HarmonicAsh/Flinders_OpenCat/CAD components/Pi3B_spacer_R_switch.stl

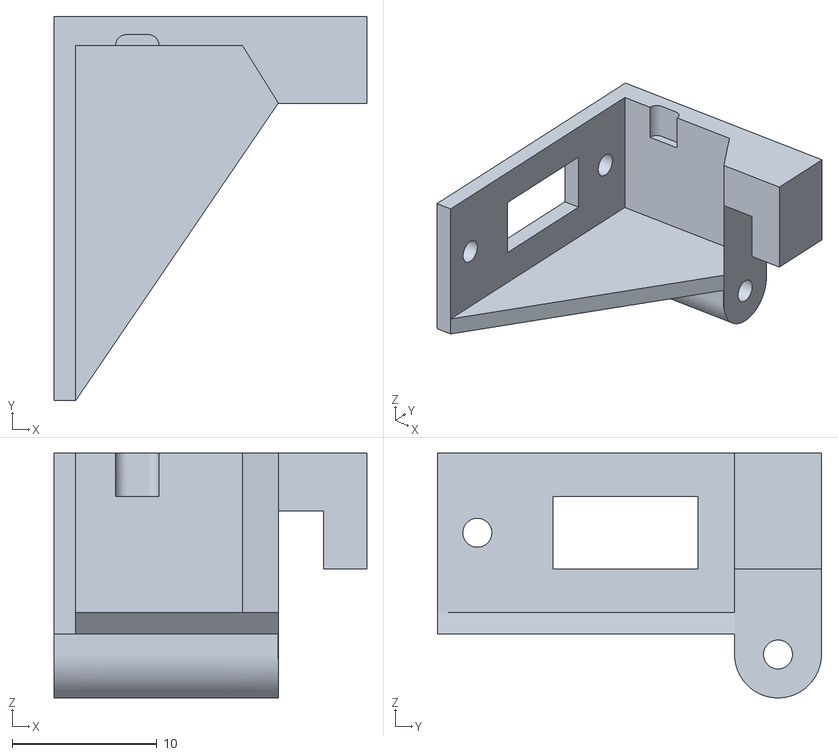
[picture p21: CAD file, 2023-02-03]
CAD components/Pi3B_spacer_R_switch.stl
21.6 x 26.5 x 16.9
