HarmonicAsh/Flinders_OpenCat/CAD components/battery mount rear.stl

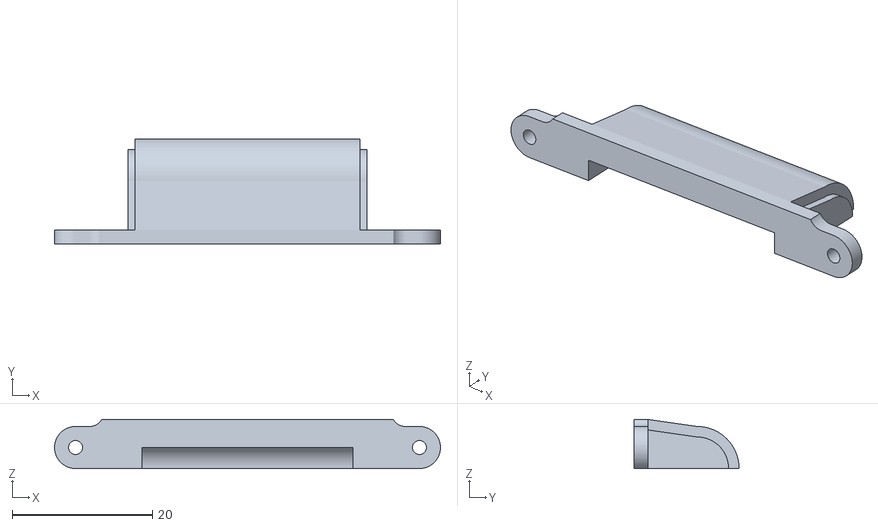
[picture p22: CAD file, 2023-01-31]
CAD components/battery mount rear.stl
55.0 x 15.0 x 7.00
