HarmonicAsh/Flinders_OpenCat/CAD components/NybbleDIY/Controller_Mount.stl

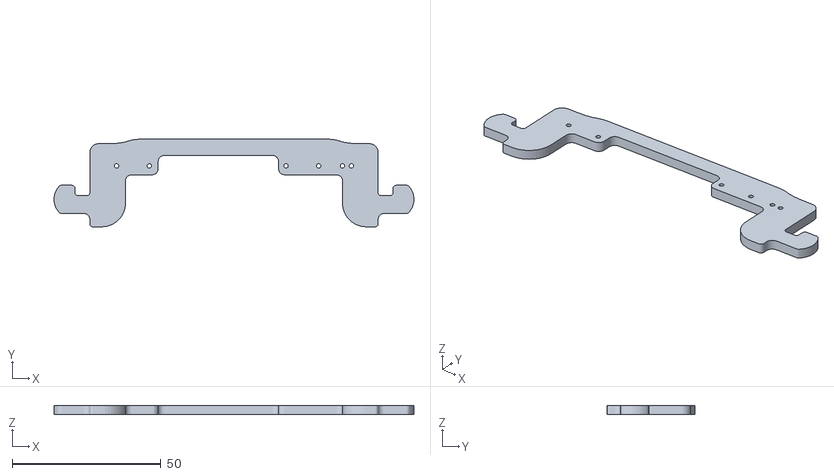
[picture p23: CAD file, 2023-01-29]
CAD components/NybbleDIY/Controller_Mount.stl
121.1 x 29.5 x 3.00
