HarmonicAsh/Flinders_OpenCat/CAD components/Battery mount front.stl

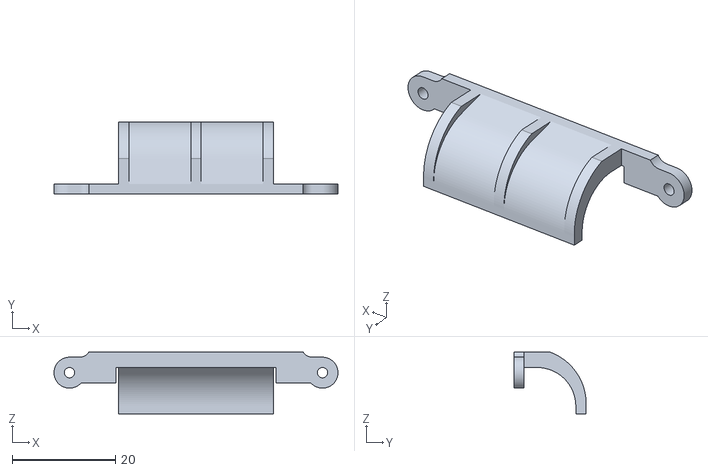
[picture p24: CAD file, 2023-01-31]
CAD components/Battery mount front.stl
55.0 x 14.0 x 12.0
