HarmonicAsh/Flinders_OpenCat/CAD components/NybbleDIY/Whiskers.stl

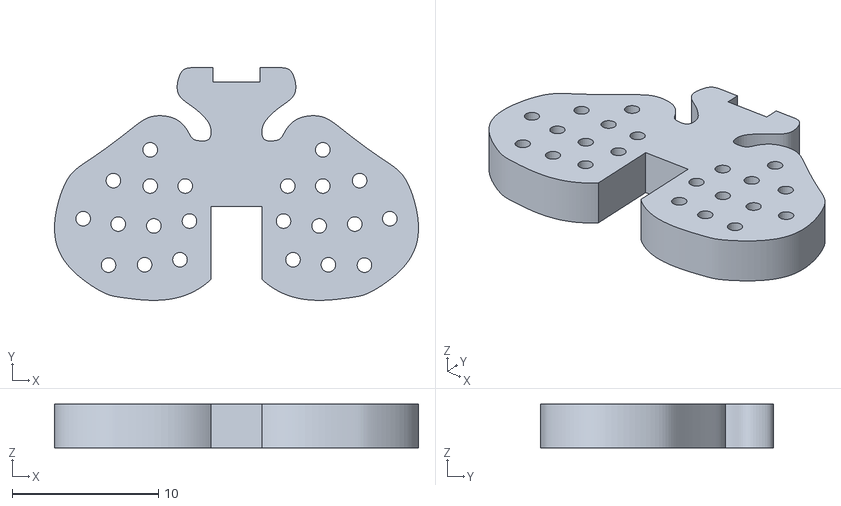
[picture p25: CAD file, 2023-01-29]
CAD components/NybbleDIY/Whiskers.stl
24.9 x 15.9 x 3.00
