HarmonicAsh/Flinders_OpenCat/CAD components/Base_modded.stl

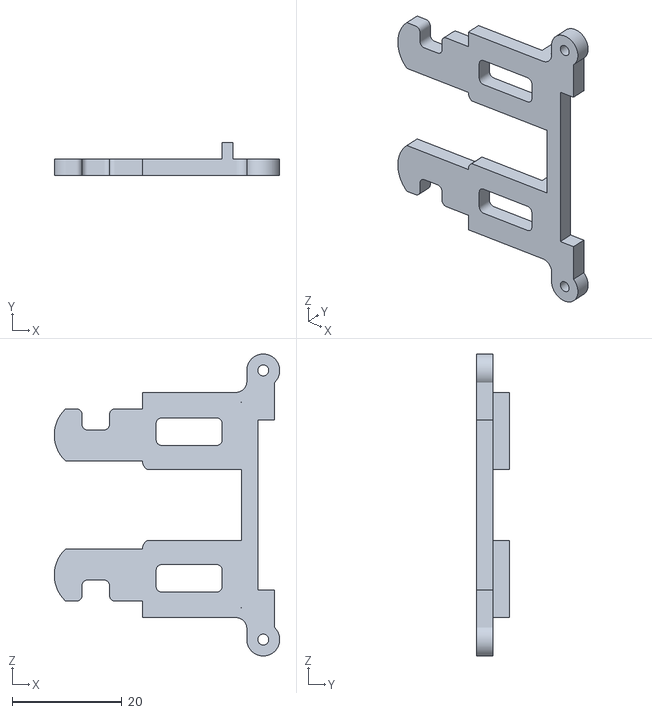
[picture p26: CAD file, 2023-01-31]
CAD components/Base_modded.stl
41.1 x 6.00 x 55.0
