HarmonicAsh/Flinders_OpenCat/CAD components/NybbleDIY/Thigh_Test_4.9mm.stl

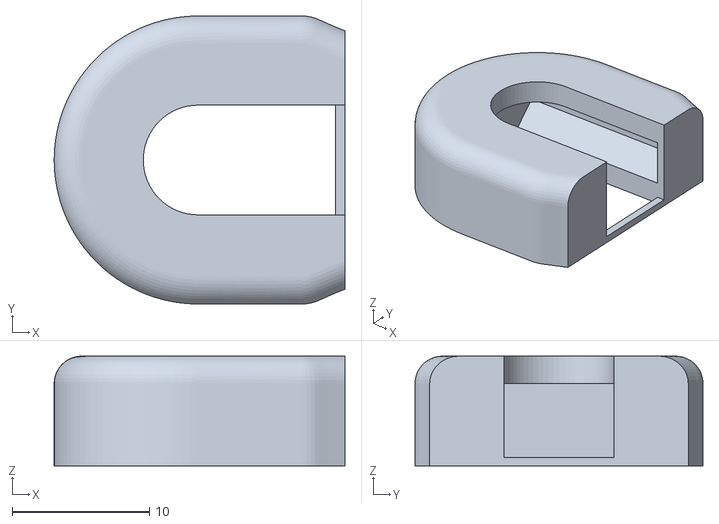
[picture p27: CAD file, 2023-01-29]
CAD components/NybbleDIY/Thigh_Test_4.9mm.stl
21.2 x 21.0 x 8.00
