HarmonicAsh/Flinders_OpenCat/CAD components/Pi3B_spacer_R.stl

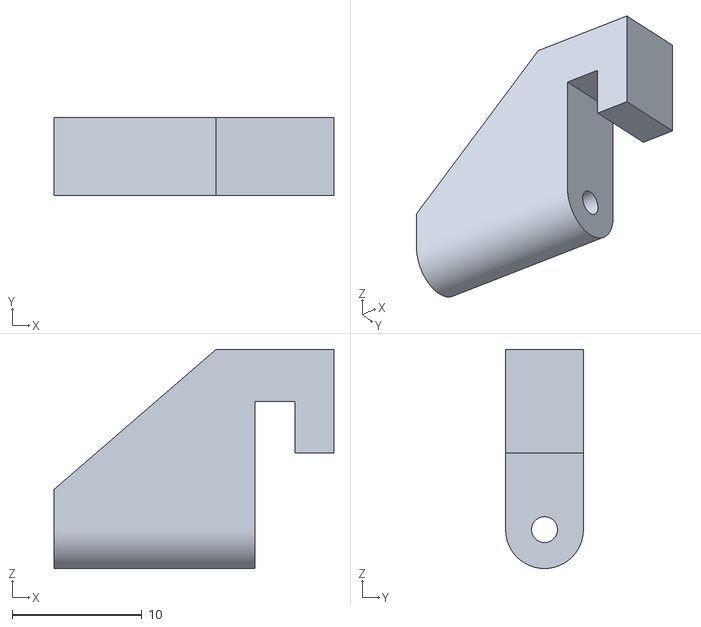
[picture p28: CAD file, 2023-01-30]
CAD components/Pi3B_spacer_R.stl
21.6 x 6.00 x 16.9
