HarmonicAsh/Flinders_OpenCat/CAD components/Battery_holder_upper.stl

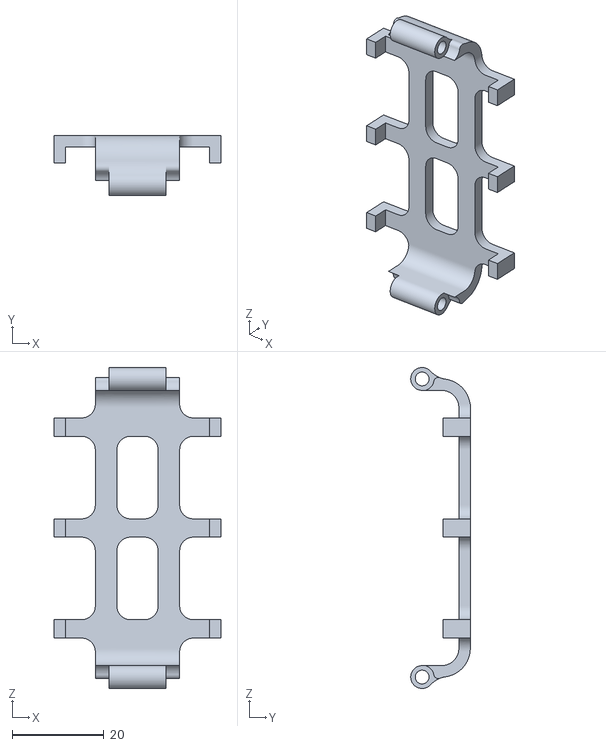
[picture p29: CAD file, 2023-01-30]
CAD components/Battery_holder_upper.stl
36.4 x 13.0 x 70.0
