HarmonicAsh/Flinders_OpenCat/CAD components/NybbleDIY/Neck_Side_Plate.stl

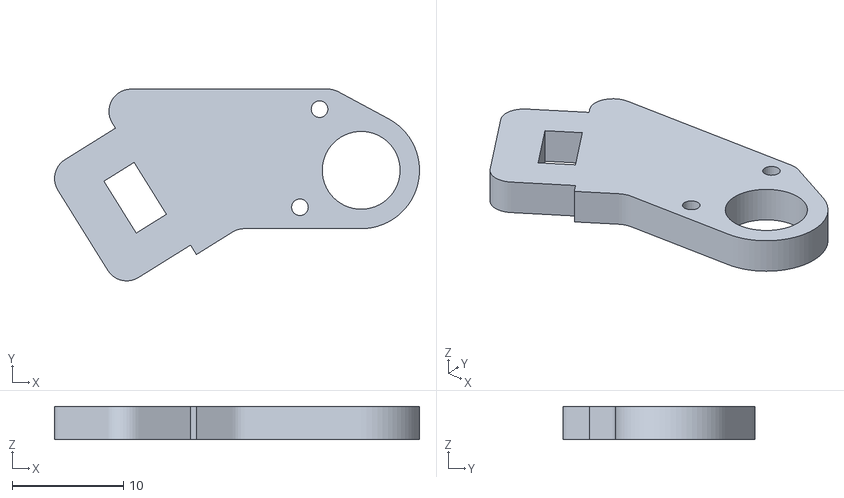
[picture p30: CAD file, 2023-01-29]
CAD components/NybbleDIY/Neck_Side_Plate.stl
32.8 x 17.3 x 3.00
