HarmonicAsh/Flinders_OpenCat/CAD components/Battery_holer_lower.stl

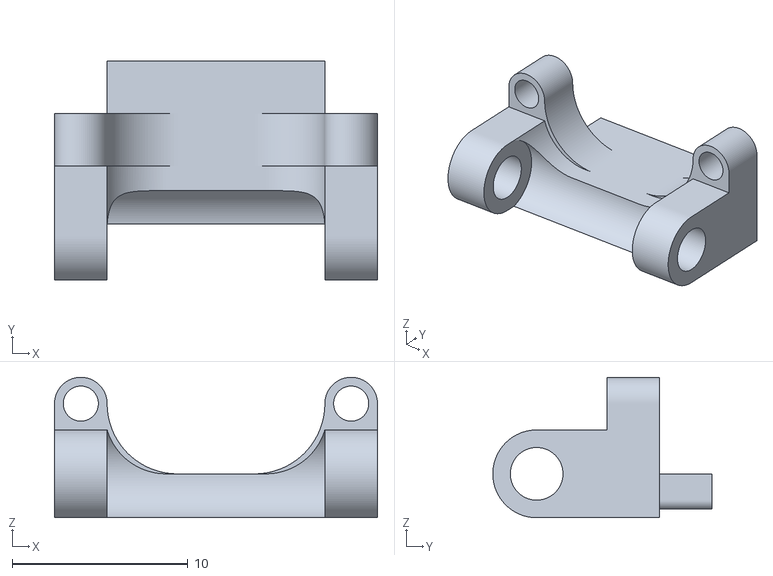
[picture p31: CAD file, 2023-01-30]
CAD components/Battery_holer_lower.stl
18.4 x 12.5 x 8.00
