HarmonicAsh/Flinders_OpenCat/CAD components/NybbleDIY/Tail.stl

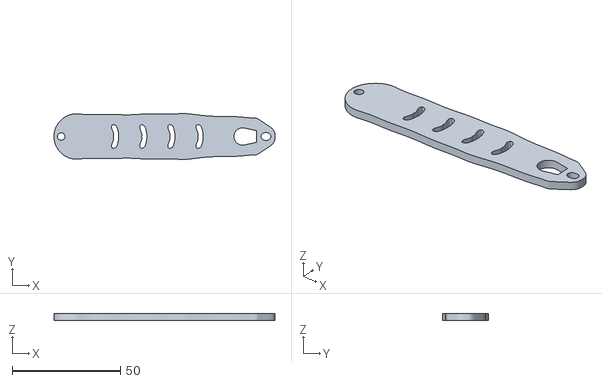
[picture p32: CAD file, 2023-01-29]
CAD components/NybbleDIY/Tail.stl
102.0 x 21.2 x 3.00
