HarmonicAsh/Flinders_OpenCat/CAD components/NybbleDIY/Chest_Hips.stl

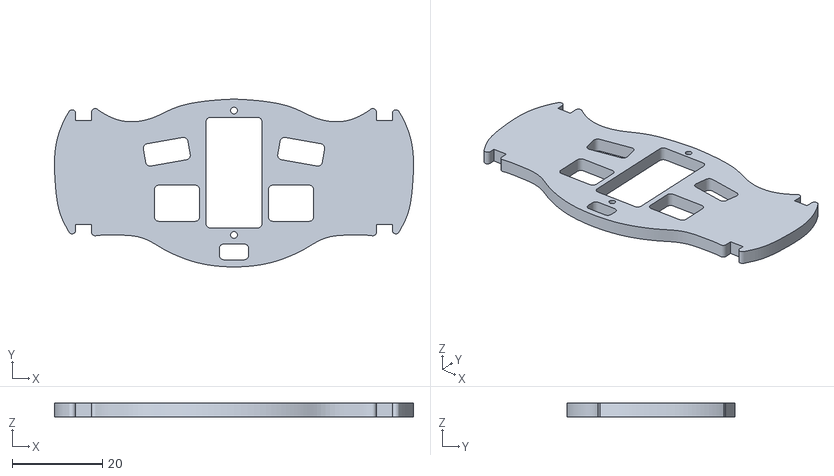
[picture p33: CAD file, 2023-01-29]
CAD components/NybbleDIY/Chest_Hips.stl
79.4 x 37.1 x 3.00
