HarmonicAsh/Flinders_OpenCat/CAD components/Pi_mount.stl

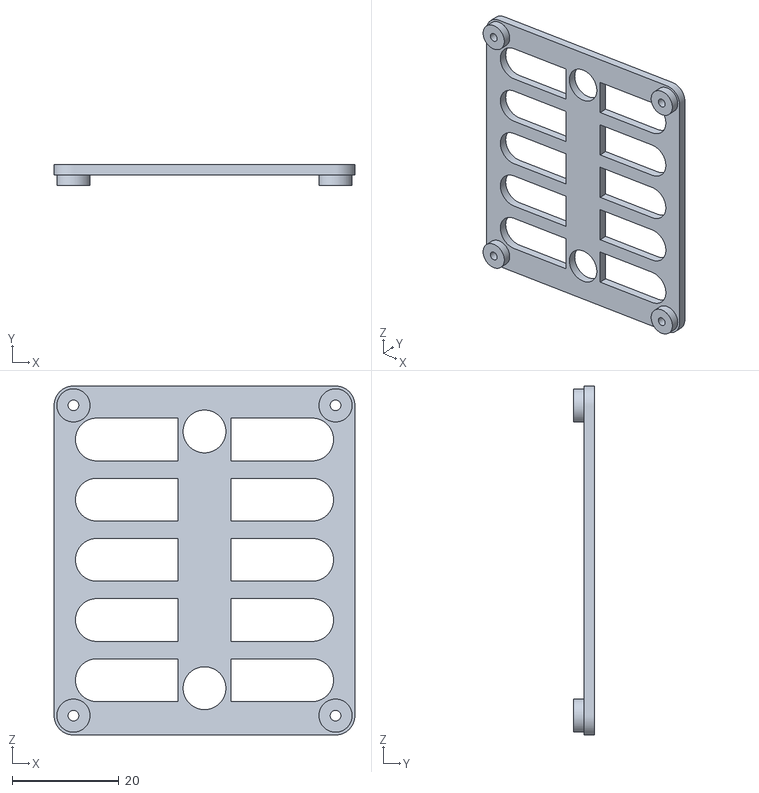
[picture p34: CAD file, 2023-01-29]
CAD components/Pi_mount.stl
56.2 x 4.00 x 65.2
