HarmonicAsh/Flinders_OpenCat/CAD components/NybbleDIY/BellyPlate.stl

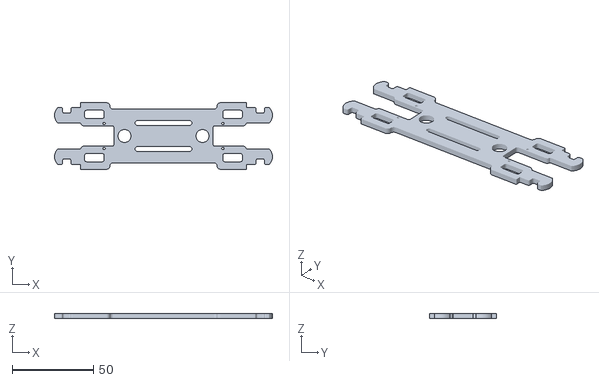
[picture p35: CAD file, 2023-01-29]
CAD components/NybbleDIY/BellyPlate.stl
134.1 x 41.0 x 3.00
