HarmonicAsh/Flinders_OpenCat/CAD components/Pi_lid.stl

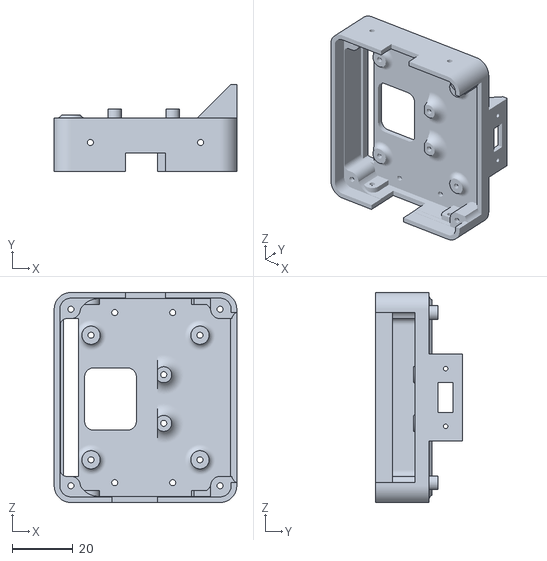
[picture p36: CAD file, 2023-01-29]
CAD components/Pi_lid.stl
60.0 x 28.5 x 69.0
