HarmonicAsh/Flinders_OpenCat/CAD components/NybbleDIY/Eyes.stl

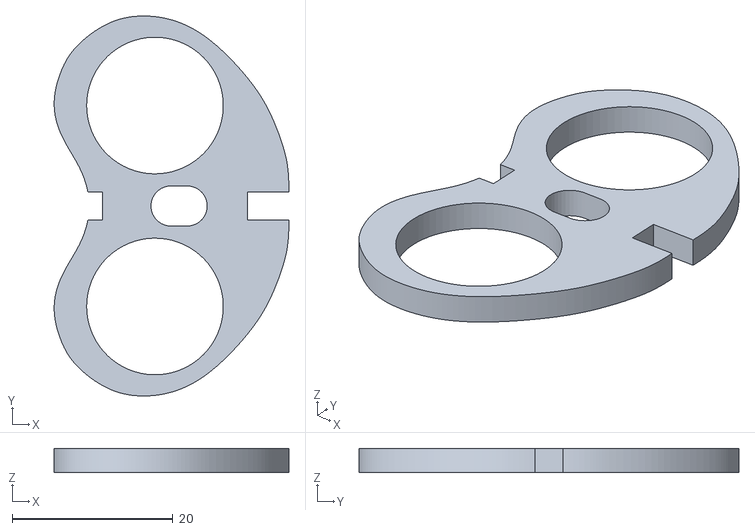
[picture p37: CAD file, 2023-01-29]
CAD components/NybbleDIY/Eyes.stl
29.2 x 47.3 x 3.00
