HarmonicAsh/Flinders_OpenCat/CAD components/Pi3B_spacer_F.stl

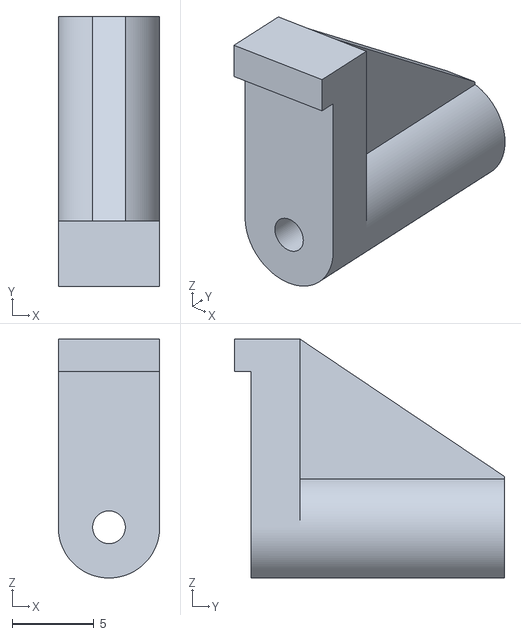
[picture p38: CAD file, 2023-01-29]
CAD components/Pi3B_spacer_F.stl
6.20 x 16.5 x 14.6
