HarmonicAsh/Flinders_OpenCat/CAD components/Braces.stl

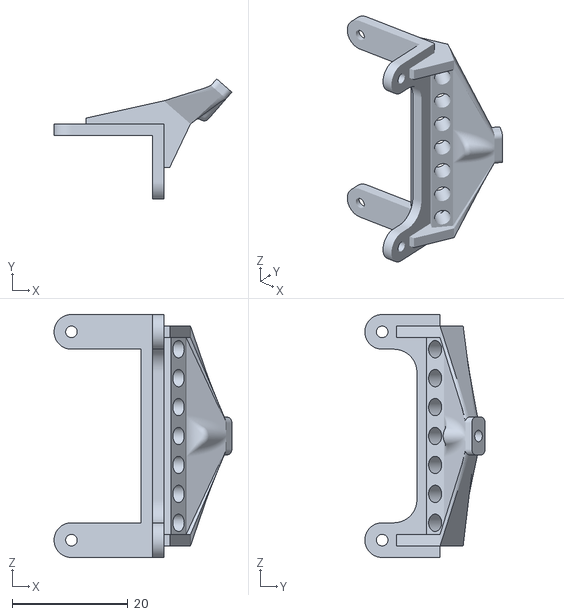
[picture p39: CAD file, 2023-01-29]
CAD components/Braces.stl
30.7 x 20.8 x 42.0
