HarmonicAsh/Flinders_OpenCat/CAD components/NybbleDIY/Skull.stl

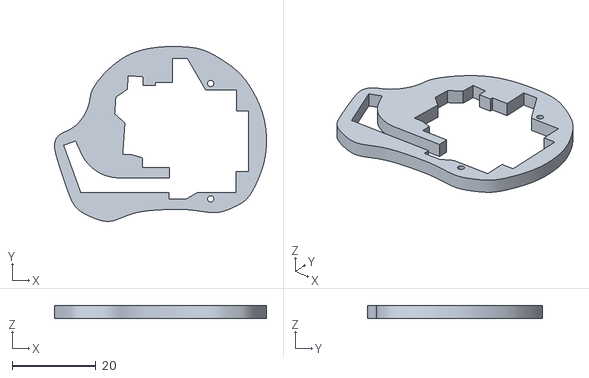
[picture p40: CAD file, 2023-01-29]
CAD components/NybbleDIY/Skull.stl
50.5 x 41.7 x 3.00
