HarmonicAsh/Flinders_OpenCat/CAD components/dowel.stl

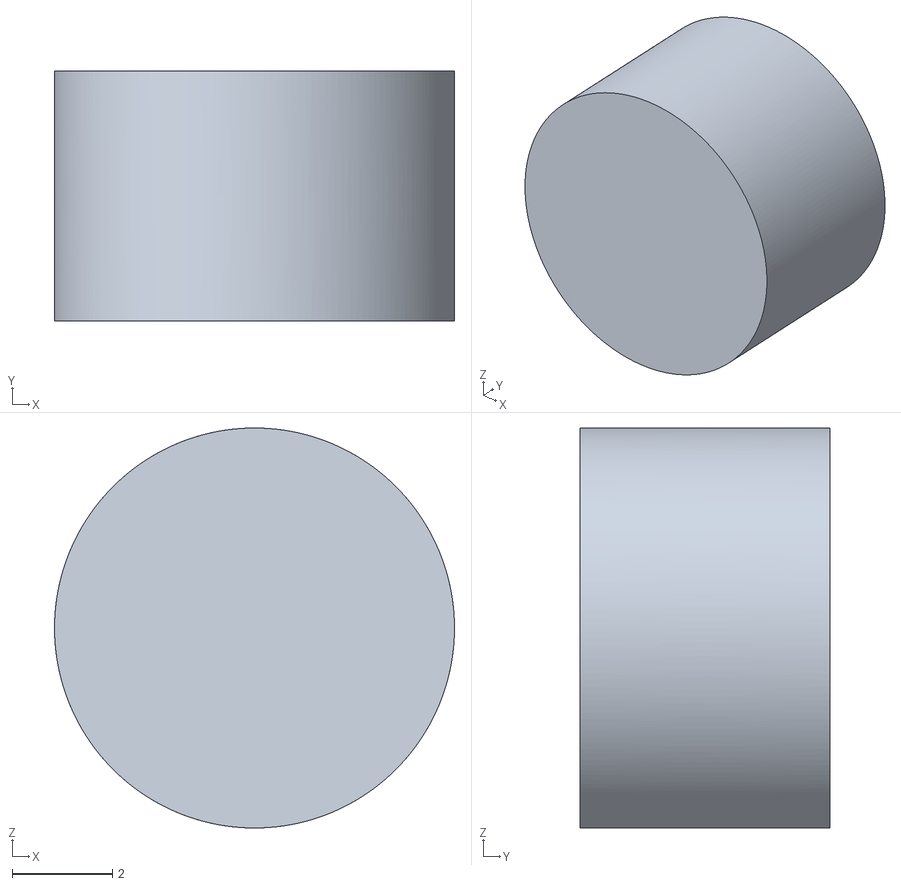
[picture p41: CAD file, 2023-01-29]
CAD components/dowel.stl
8.00 x 5.00 x 8.00
