HarmonicAsh/Flinders_OpenCat/CAD components/NybbleDIY/Shoulder.stl

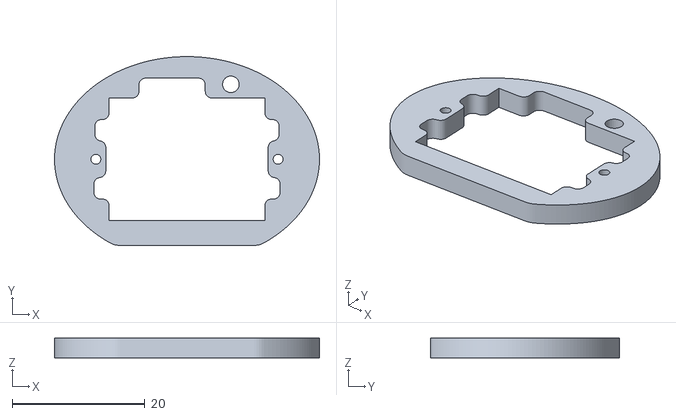
[picture p42: CAD file, 2023-01-29]
CAD components/NybbleDIY/Shoulder.stl
40.0 x 28.5 x 3.00
