HarmonicAsh/Flinders_OpenCat/CAD components/NybbleDIY/Neck_Lock.stl

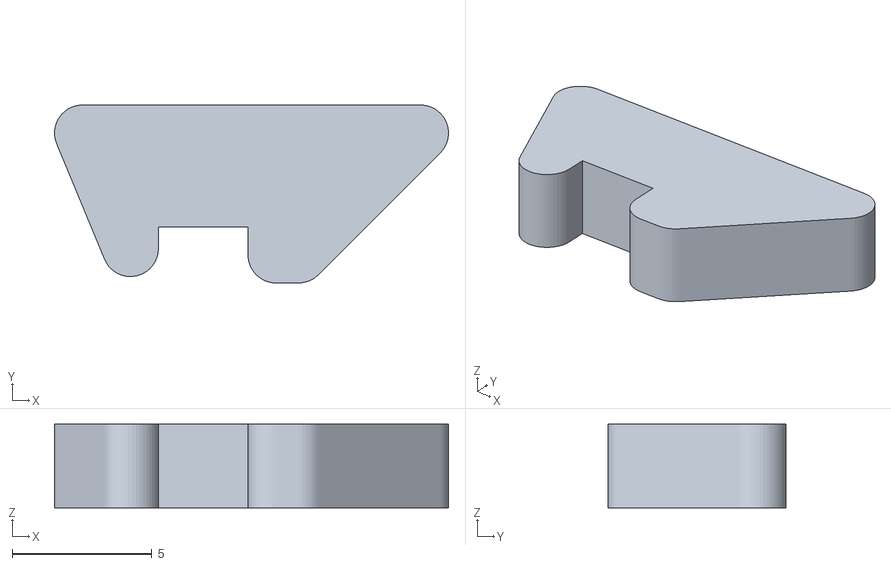
[picture p43: CAD file, 2023-01-29]
CAD components/NybbleDIY/Neck_Lock.stl
14.1 x 6.36 x 3.00
