HarmonicAsh/Flinders_OpenCat/CAD components/Spine_major.stl

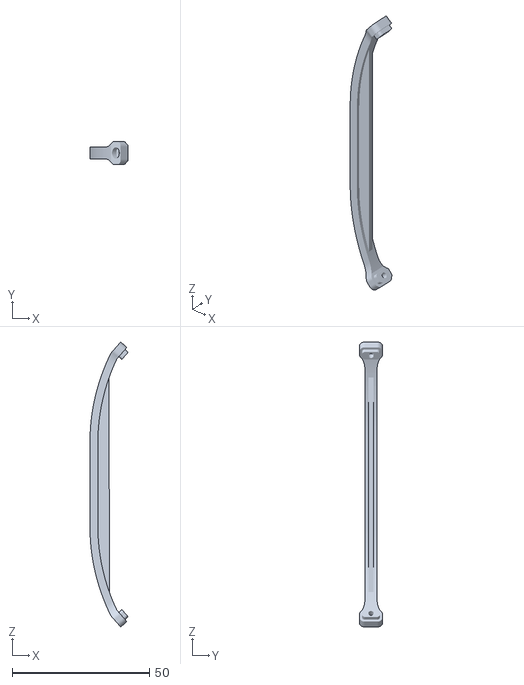
[picture p44: CAD file, 2023-01-29]
CAD components/Spine_major.stl
14.0 x 8.50 x 103.9
