HarmonicAsh/Flinders_OpenCat/CAD components/NybbleDIY/Chin.stl

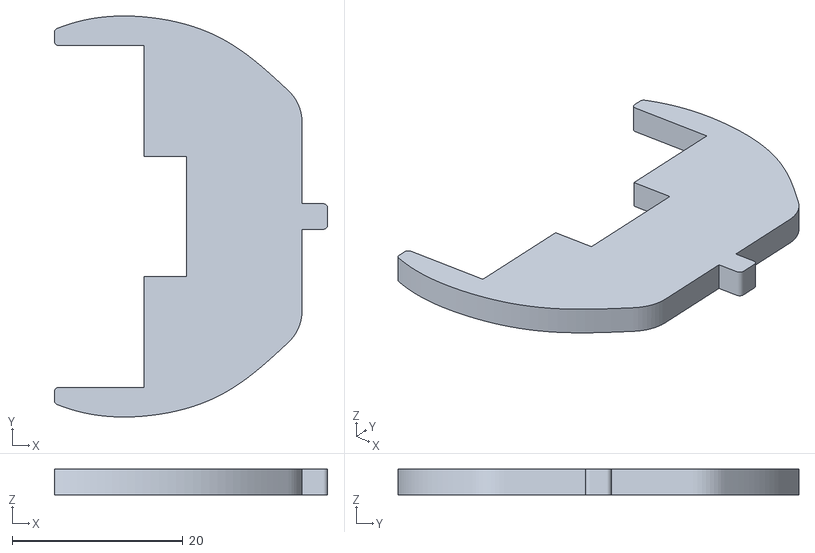
[picture p45: CAD file, 2023-01-29]
CAD components/NybbleDIY/Chin.stl
32.0 x 46.9 x 3.00
