HarmonicAsh/Flinders_OpenCat/CAD components/NybbleDIY/Tail_Wheel.stl

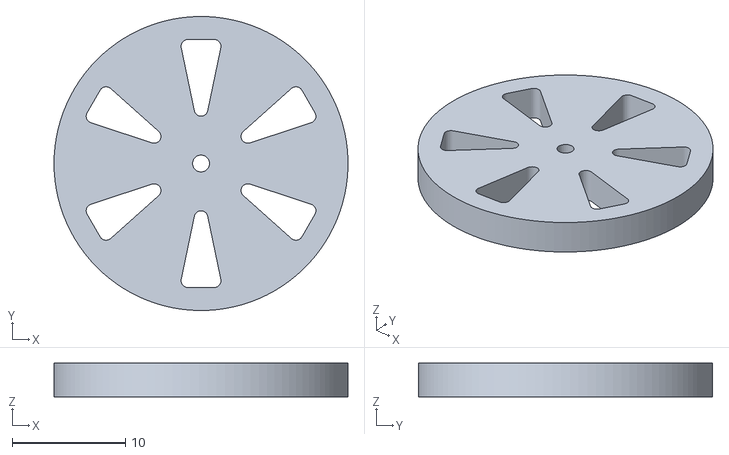
[picture p46: CAD file, 2023-01-29]
CAD components/NybbleDIY/Tail_Wheel.stl
26.0 x 26.0 x 3.00
