HarmonicAsh/Flinders_OpenCat/CAD components/NybbleDIY/Head_Spring_3.0_.4.stl

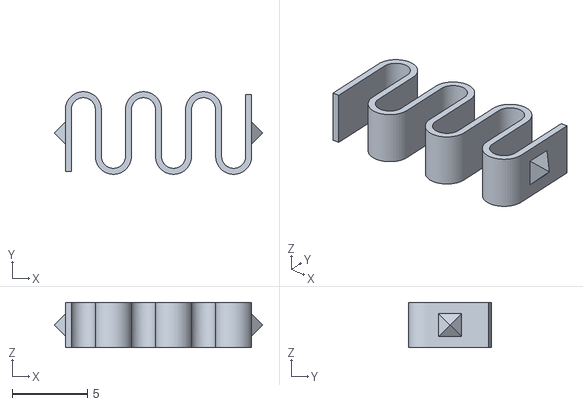
[picture p47: CAD file, 2023-01-29]
CAD components/NybbleDIY/Head_Spring_3.0_.4.stl
13.9 x 5.50 x 3.00
