HarmonicAsh/Flinders_OpenCat/CAD components/NybbleDIY/Ears.stl

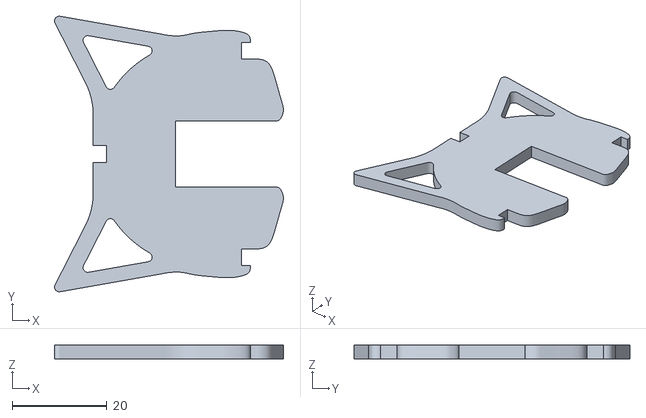
[picture p48: CAD file, 2023-01-29]
CAD components/NybbleDIY/Ears.stl
48.3 x 58.1 x 3.00
