HarmonicAsh/Flinders_OpenCat/CAD components/NybbleDIY/Forearm.stl

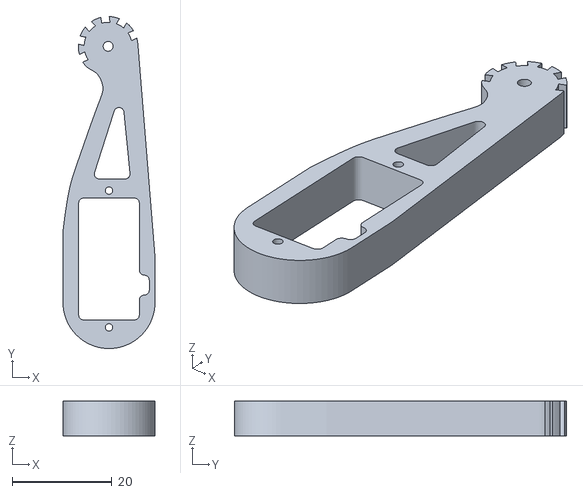
[picture p49: CAD file, 2023-01-29]
CAD components/NybbleDIY/Forearm.stl
18.5 x 66.7 x 7.00
