HarmonicAsh/Flinders_OpenCat/OpenCat1801/serialMaster/test.py

import time


def test_embed(int):
    if int == 1:
        number = 0
    elif int == 2:
        number += 
        print("Embedded number = ", number)


print("Running test...")
test_embed(1)

while True:
    test_embed(2)
    time.sleep(1)
